Aightech/FSR_array/models/KX134_array/KX134_array.png

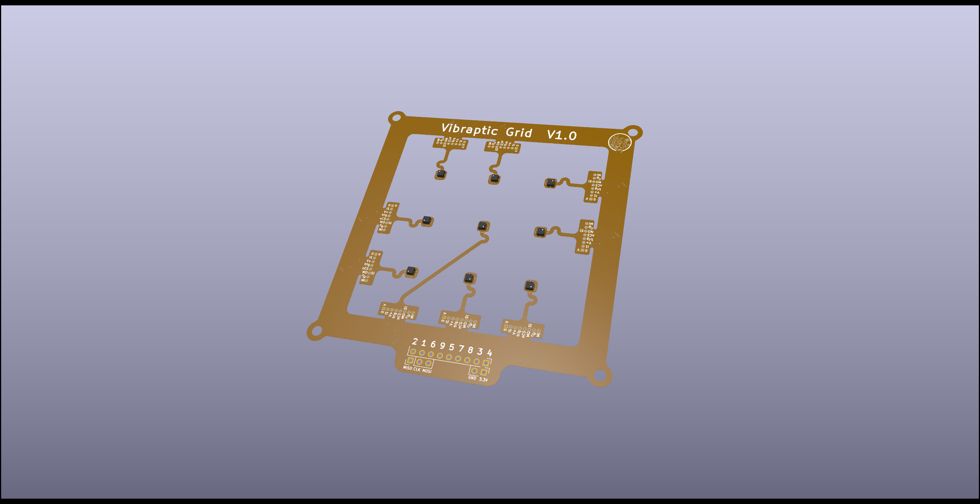
models/KX134_array/KX134_array.png
