Aightech/FSR_array/models/SW/letters/letter_Chard4.STL

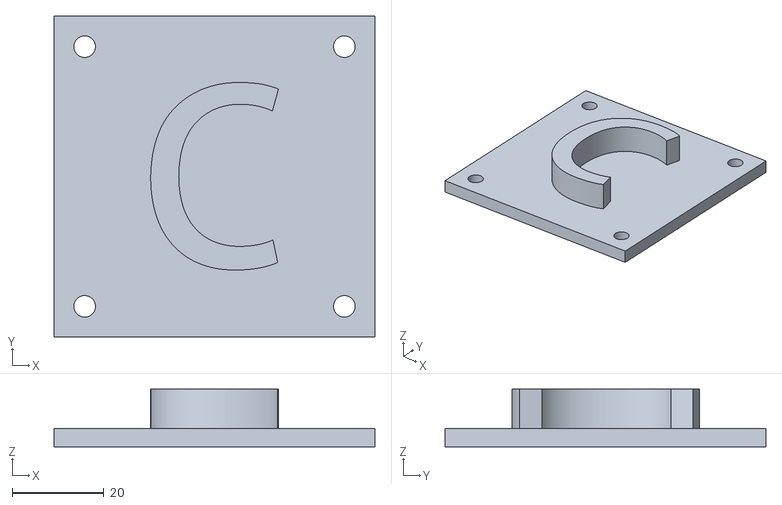
[picture p18: CAD file, 2022-10-25]
models/SW/letters/letter_Chard4.STL
70.0 x 70.0 x 12.6
