Aightech/FSR_array/models/SW/dumper.SLDPRT

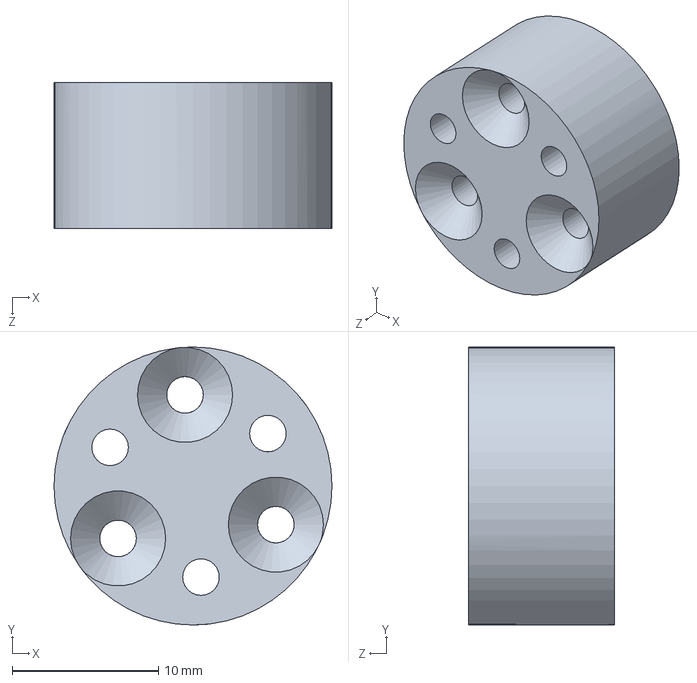
[picture p19: CAD file, 2022-10-25]
models/SW/dumper.SLDPRT
19.0 x 19.0 x 10.0 mm
