Aightech/FSR_array/models/SW/hman_support.SLDPRT

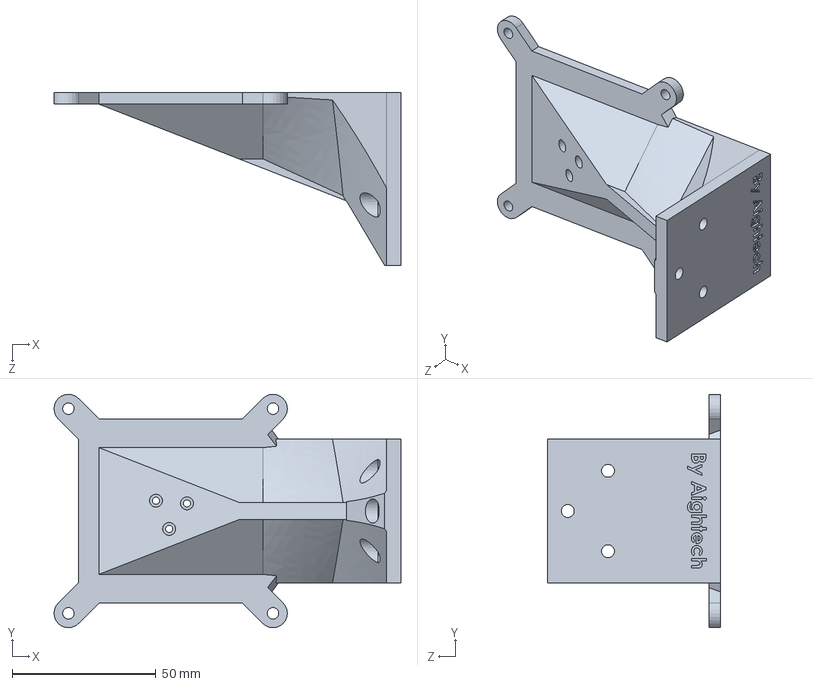
[picture p20: CAD file, 2022-10-25]
models/SW/hman_support.SLDPRT
120.5 x 81.1 x 60.0 mm
