Aightech/FSR_array/models/SW/letters/siliconeTop.SLDPRT

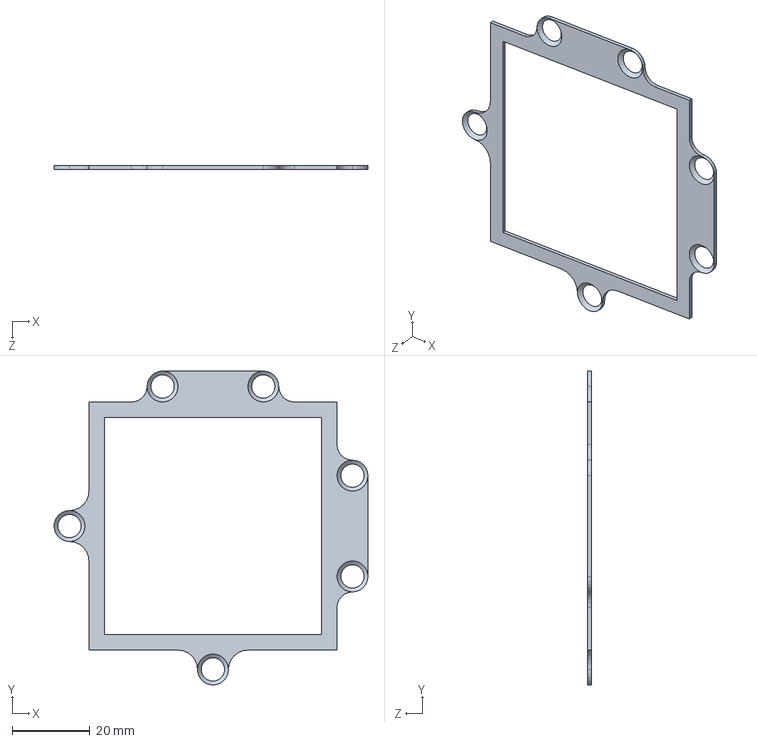
[picture p22: CAD file, 2022-10-25]
models/SW/letters/siliconeTop.SLDPRT
81.0 x 81.0 x 1.00 mm
