Aightech/FSR_array/models/SW/letters/letter_I2.STL

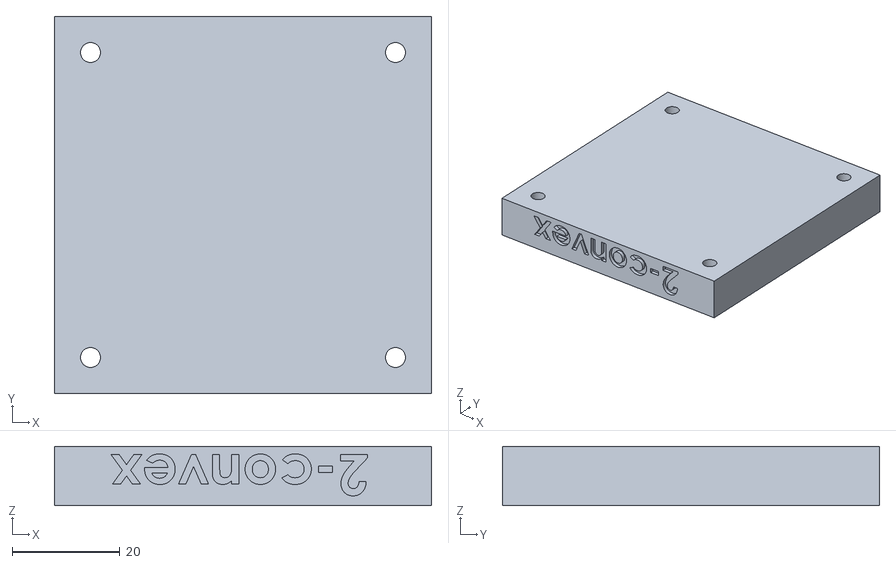
[picture p23: CAD file, 2022-10-25]
models/SW/letters/letter_I2.STL
70.0 x 70.0 x 11.0
