Aightech/FSR_array/models/SW/letters/letter_JIEhard4.STL

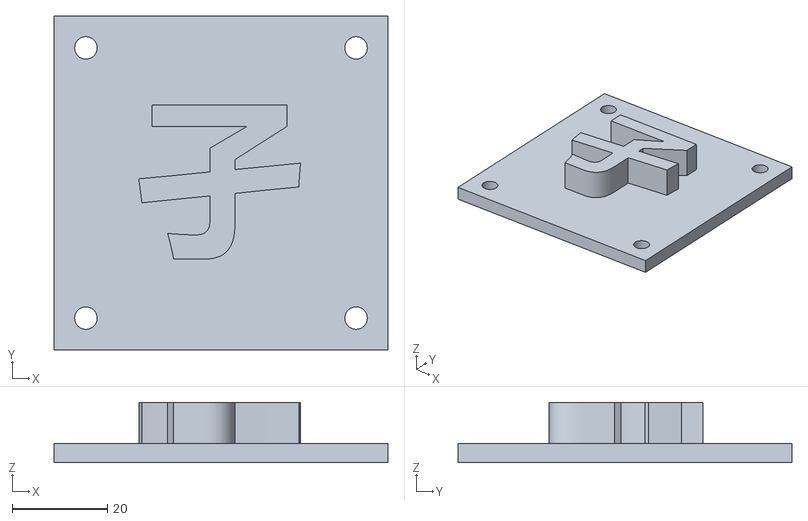
[picture p24: CAD file, 2022-10-25]
models/SW/letters/letter_JIEhard4.STL
70.0 x 70.0 x 12.6
