Aightech/FSR_array/models/SW/letters/big_letters.SLDPRT

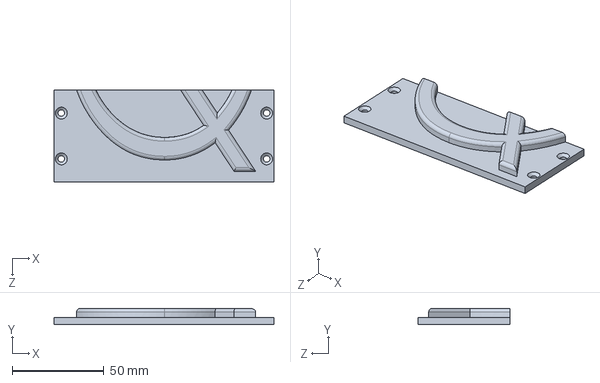
[picture p25: CAD file, 2022-10-25]
models/SW/letters/big_letters.SLDPRT
120.0 x 9.00 x 50.0 mm
