Aightech/FSR_array/models/SW/letters/siliconeTop_thin.STL

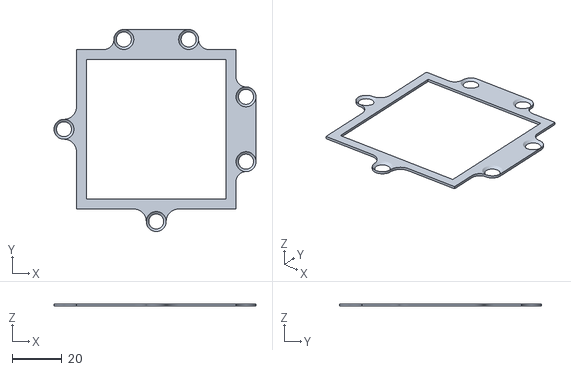
[picture p26: CAD file, 2022-10-25]
models/SW/letters/siliconeTop_thin.STL
81.0 x 81.0 x 1.00
