Aightech/FSR_array/models/SW/letters/letter_Q4.STL

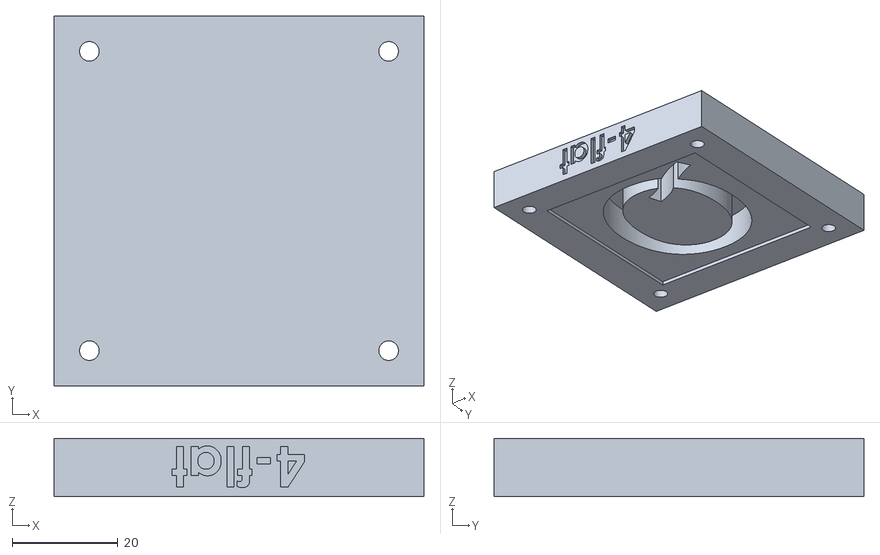
[picture p27: CAD file, 2022-10-25]
models/SW/letters/letter_Q4.STL
70.0 x 70.0 x 11.0
