Aightech/FSR_array/models/SW/letters/letterssilicone_holder.SLDPRT

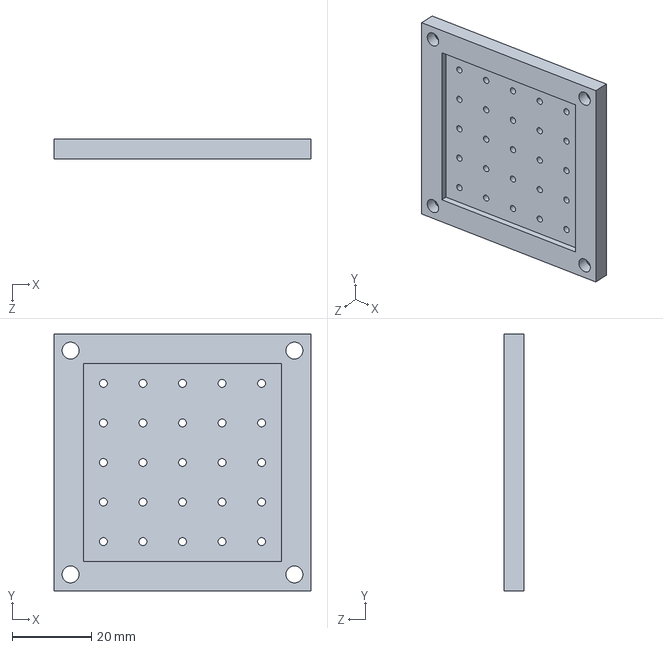
[picture p28: CAD file, 2022-10-25]
models/SW/letters/letterssilicone_holder.SLDPRT
65.0 x 65.0 x 5.00 mm
