Aightech/FSR_array/models/SW/letters/letter_Chard1.STL

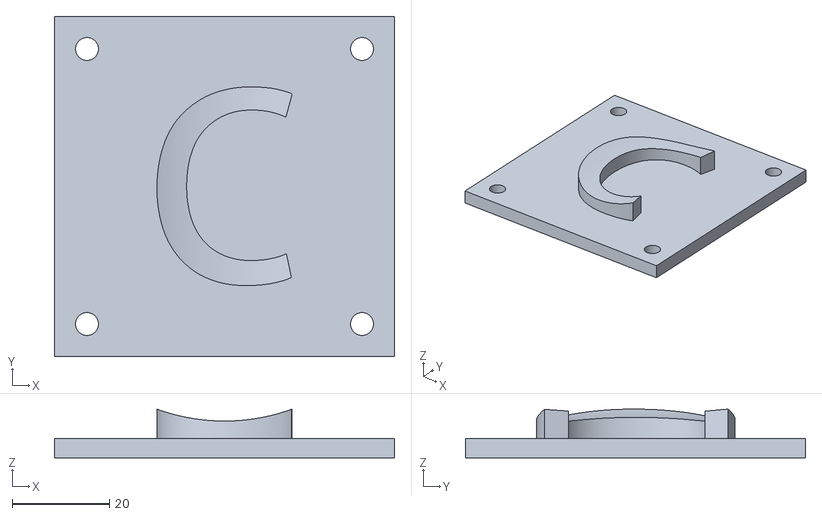
[picture p29: CAD file, 2022-10-25]
models/SW/letters/letter_Chard1.STL
70.0 x 70.0 x 10.1
