Aightech/FSR_array/models/SW/letters/letter_Qhard3.STL

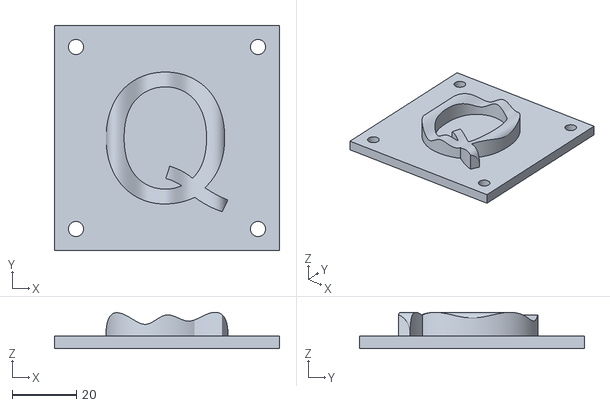
[picture p30: CAD file, 2022-10-25]
models/SW/letters/letter_Qhard3.STL
70.0 x 70.0 x 11.3
